LjungrennAudio/ryomodular.com_flipflop-i/docs/Conversion of Flip-flops from one flip-flop to Another_files/sequential-seq40.gif

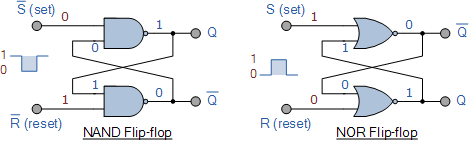
docs/Conversion of Flip-flops from one flip-flop to Another_files/sequential-seq40.gif
