LjungrennAudio/ryomodular.com_flipflop-i/docs/Conversion of Flip-flops from one flip-flop to Another_files/sequential-seq44.gif

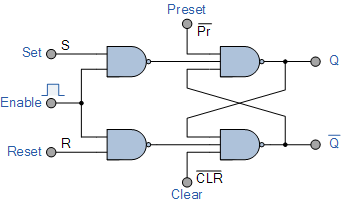
docs/Conversion of Flip-flops from one flip-flop to Another_files/sequential-seq44.gif
