LjungrennAudio/ryomodular.com_flipflop-i/flipflop.png

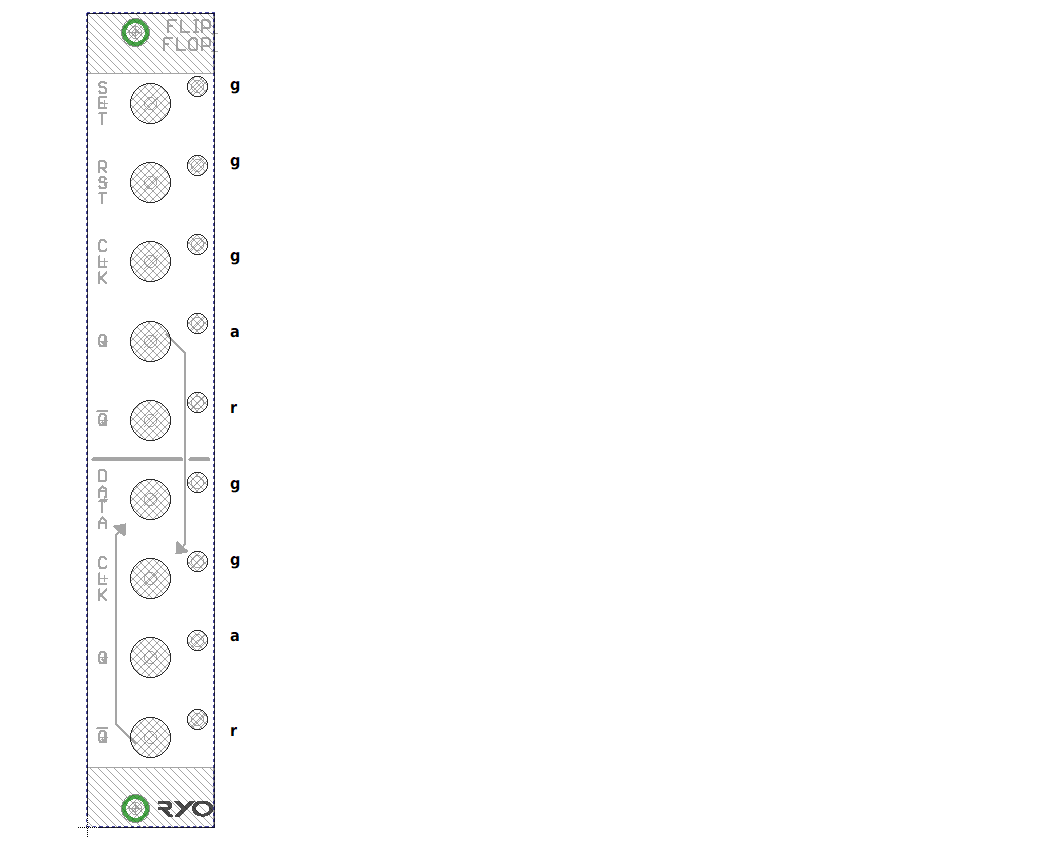
flipflop.png
